RutronikKaunas/RutAdaptBoard-UVALED/Hardware Design Files/RutAdaptBoard-UVALED Housing/IMG_20201109_120839.jpg

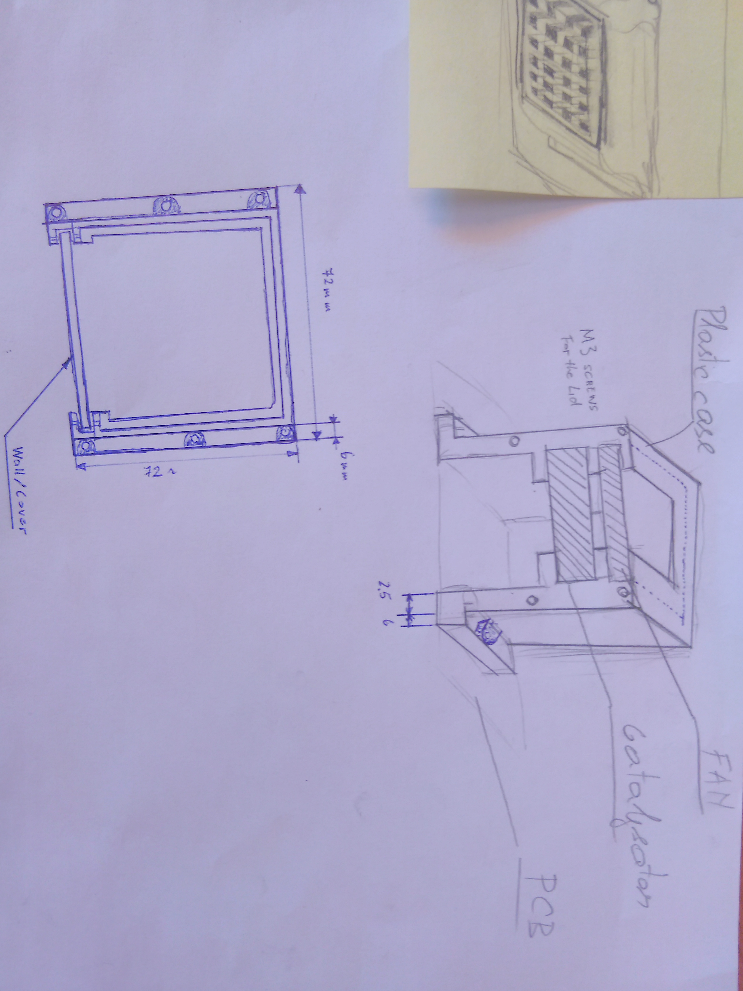
Hardware Design Files/RutAdaptBoard-UVALED Housing/IMG_20201109_120839.jpg
