RutronikKaunas/RutAdaptBoard-UVALED/Hardware Design Files/RutAdaptBoard-UVALED Housing/Render/final render.JPG

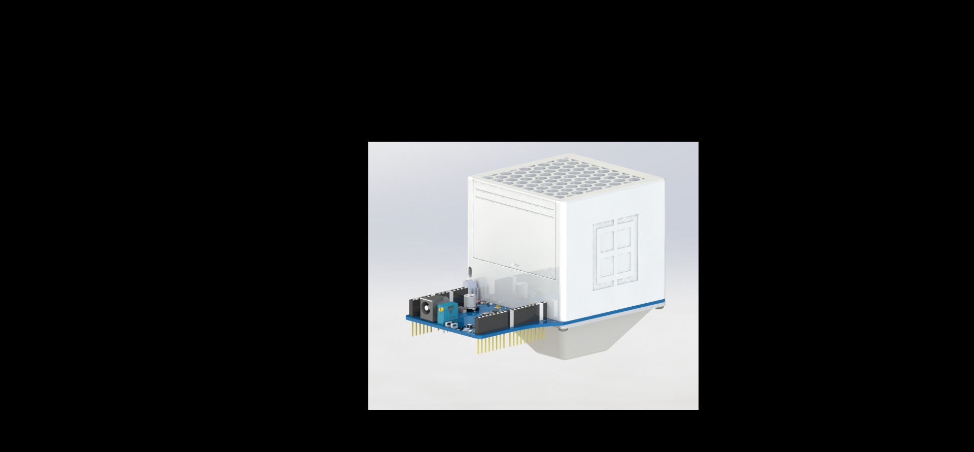
Hardware Design Files/RutAdaptBoard-UVALED Housing/Render/final render.JPG
